David-Birge-Cotte/la-spirulerie/STL/secchi.stl

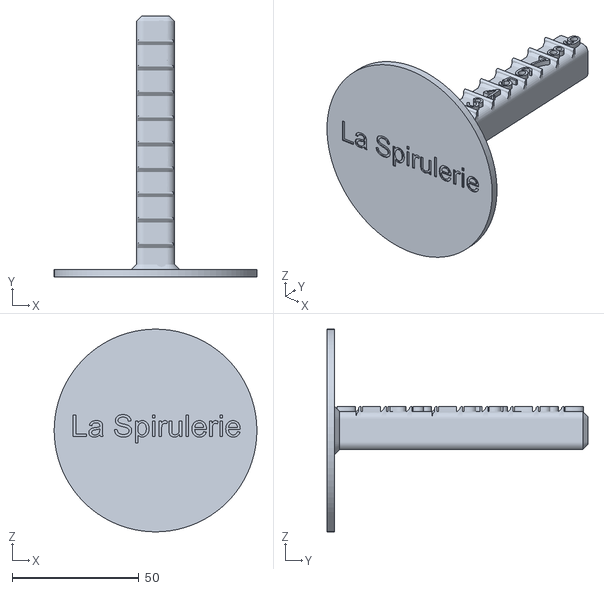
[picture p15: CAD file, 2020-11-30]
STL/secchi.stl
80.0 x 103.0 x 80.0
