David-Birge-Cotte/la-spirulerie/STL/white_glued_prints/level_indicator.stl

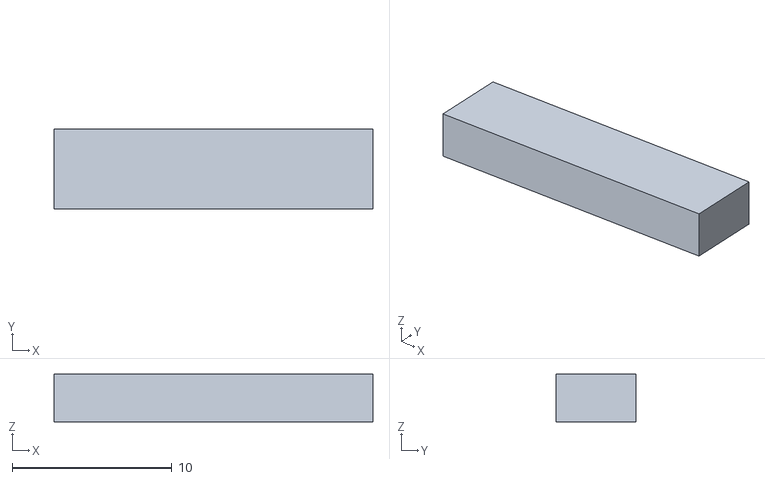
[picture p16: CAD file, 2020-11-30]
STL/white_glued_prints/level_indicator.stl
20.0 x 5.00 x 3.00
