David-Birge-Cotte/la-spirulerie/STL/couvercle/Centre/Couvercle_fermé_4mm.stl

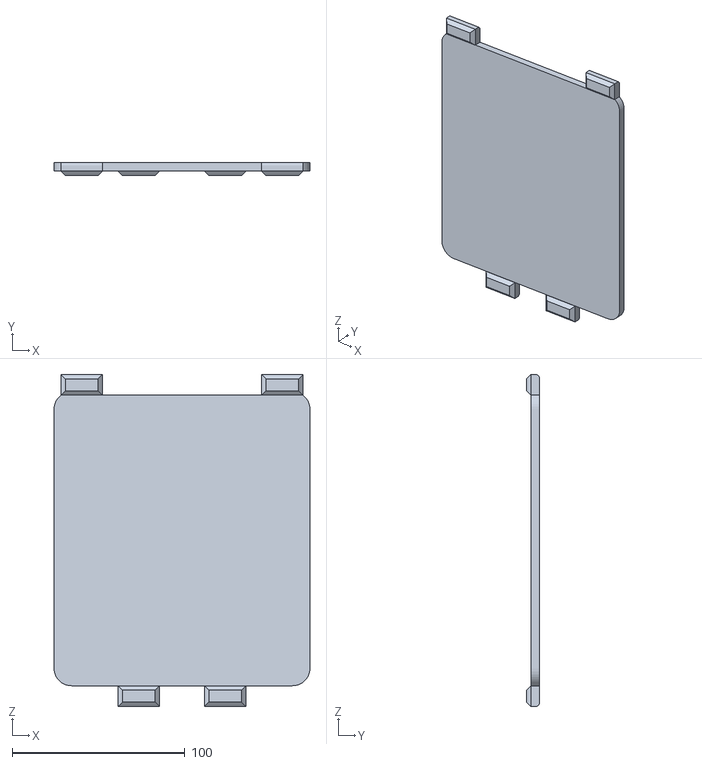
[picture p17: CAD file, 2020-11-30]
STL/couvercle/Centre/Couvercle_fermé_4mm.stl
148.0 x 7.50 x 192.0
