David-Birge-Cotte/la-spirulerie/STL/couvercle/Côté/Couvercle_protection.stl

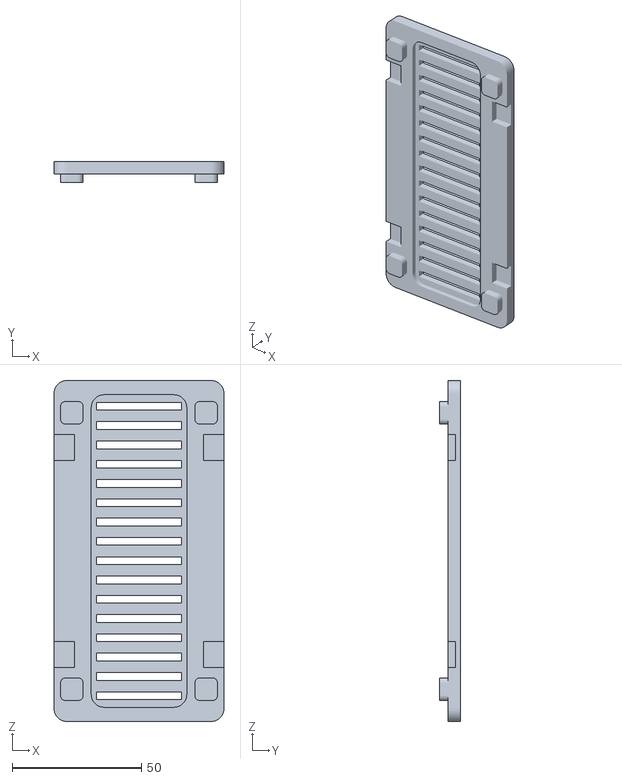
[picture p18: CAD file, 2020-11-30]
STL/couvercle/Côté/Couvercle_protection.stl
65.8 x 8.30 x 132.0
