David-Birge-Cotte/la-spirulerie/STL/couvercle/Recolte/Passoire_récolte.stl

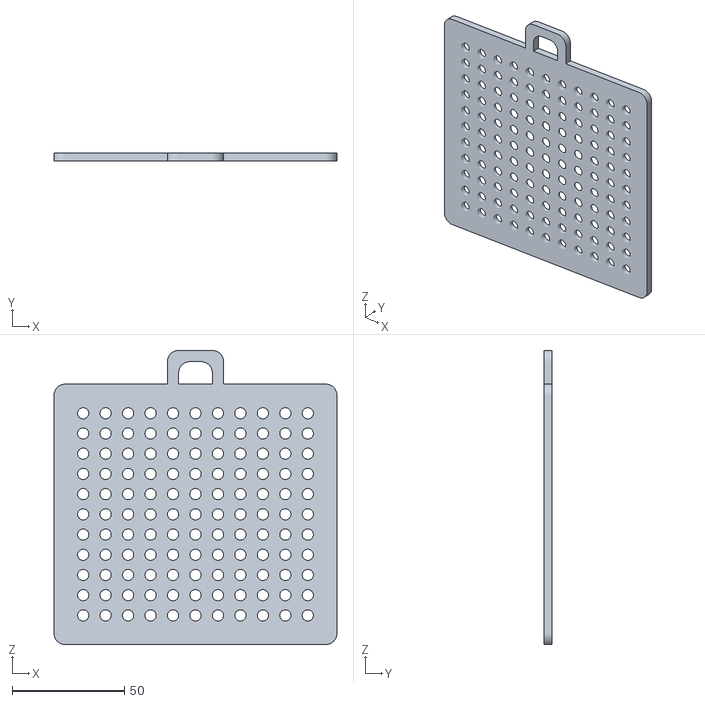
[picture p19: CAD file, 2020-11-30]
STL/couvercle/Recolte/Passoire_récolte.stl
126.0 x 3.69 x 131.0
