David-Birge-Cotte/la-spirulerie/STL/interface/standalone/interface_attache_new.stl

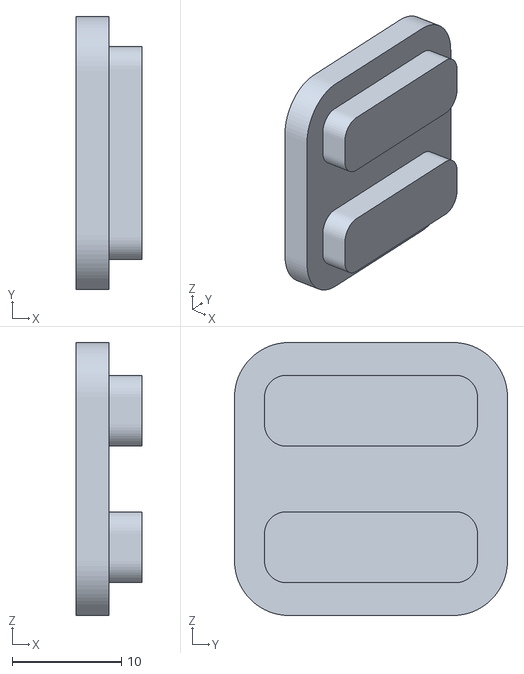
[picture p20: CAD file, 2020-11-30]
STL/interface/standalone/interface_attache_new.stl
6.00 x 25.0 x 25.0
