David-Birge-Cotte/la-spirulerie/STL/Pied.stl

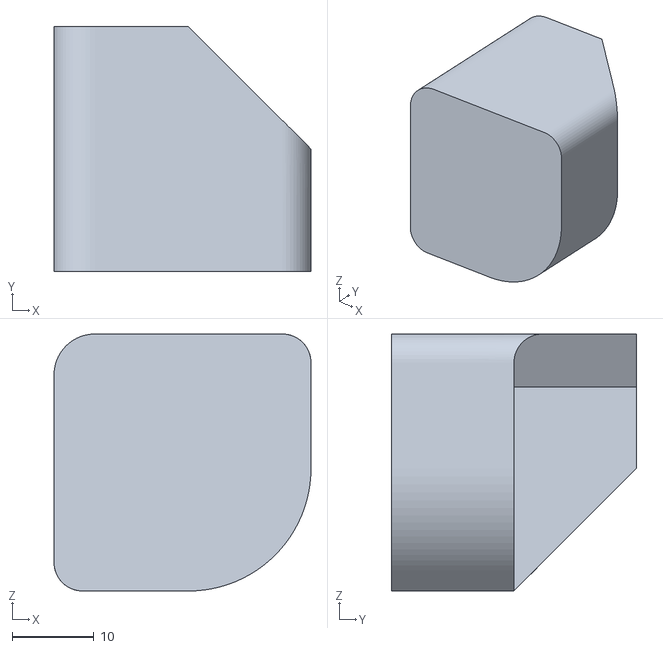
[picture p21: CAD file, 2020-11-30]
STL/Pied.stl
31.5 x 30.0 x 31.5
