David-Birge-Cotte/la-spirulerie/STL/boitier/Couvercle_Boitier_PCB.stl

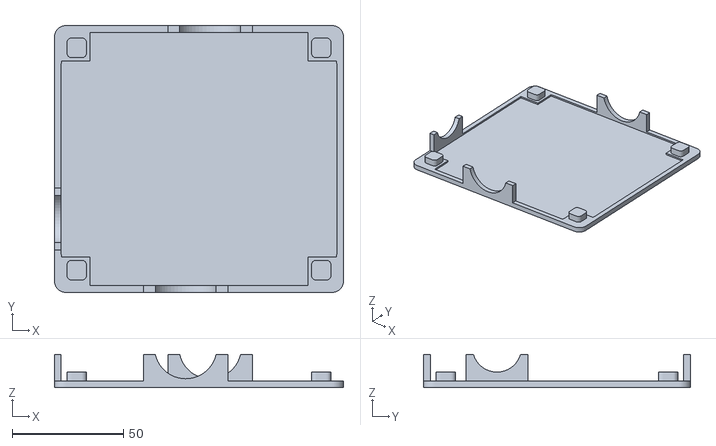
[picture p22: CAD file, 2020-11-30]
STL/boitier/Couvercle_Boitier_PCB.stl
130.0 x 120.0 x 15.0
