David-Birge-Cotte/la-spirulerie/STL/couvercle/Côté/Couvercle_protection_radiators.stl

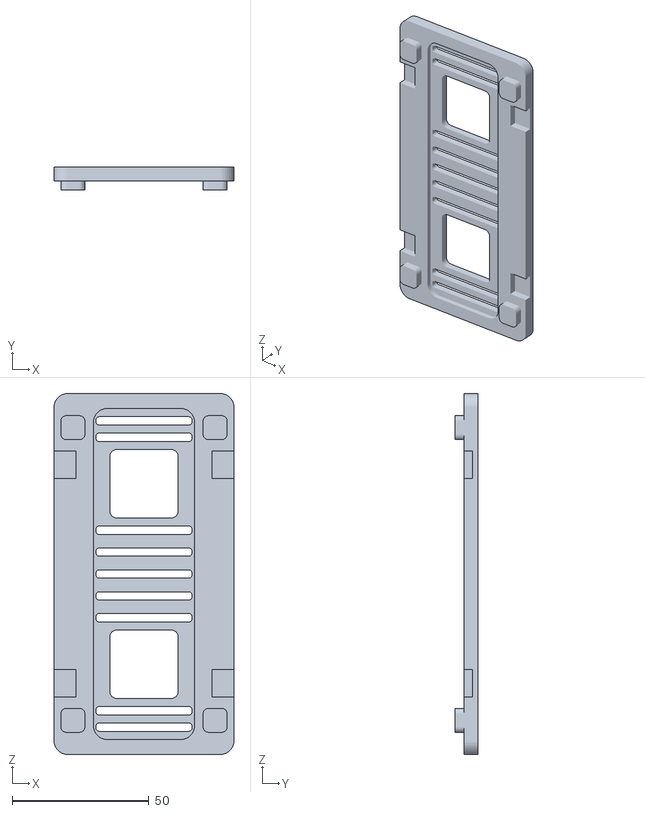
[picture p23: CAD file, 2020-11-30]
STL/couvercle/Côté/Couvercle_protection_radiators.stl
65.8 x 8.30 x 132.0
