David-Birge-Cotte/la-spirulerie/STL/interface/support_ecran.stl

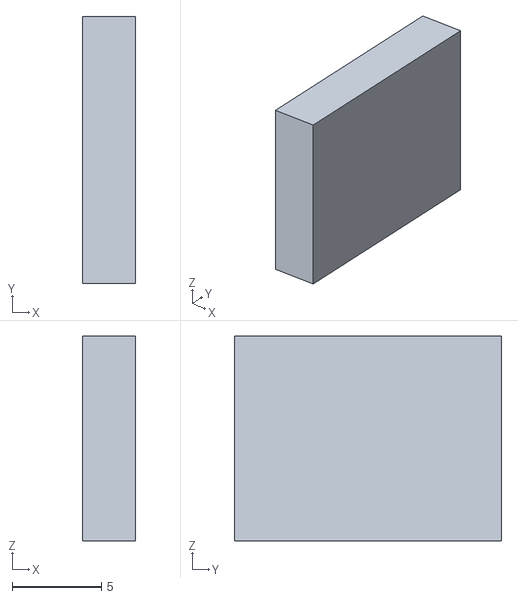
[picture p24: CAD file, 2020-11-30]
STL/interface/support_ecran.stl
3.00 x 15.0 x 11.5
