David-Birge-Cotte/la-spirulerie/STL/boitier/Porte_Boitier_standalone_8.65.stl

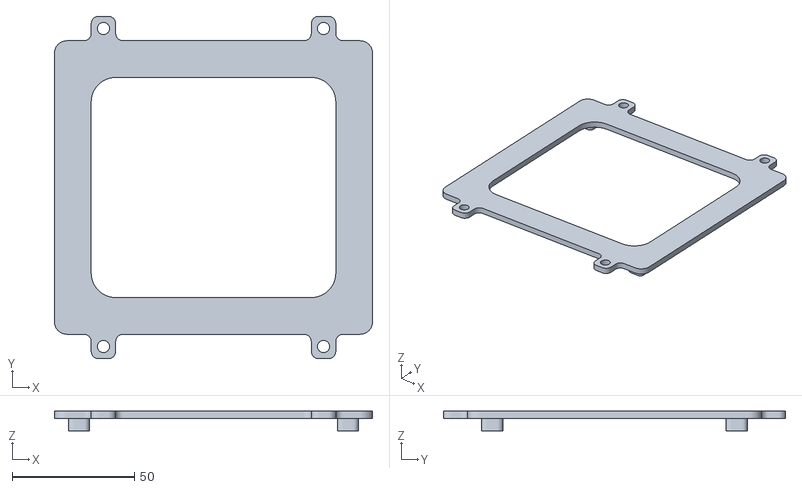
[picture p25: CAD file, 2020-11-30]
STL/boitier/Porte_Boitier_standalone_8.65.stl
130.0 x 140.0 x 8.00
