David-Birge-Cotte/la-spirulerie/STL/interface/interface_bas.stl

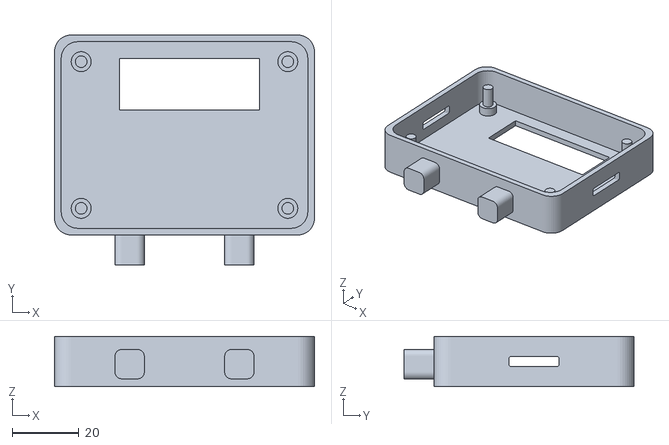
[picture p26: CAD file, 2020-11-30]
STL/interface/interface_bas.stl
78.0 x 69.0 x 15.0
